tamaroh/maggie42/image/IMG_0094.jpg

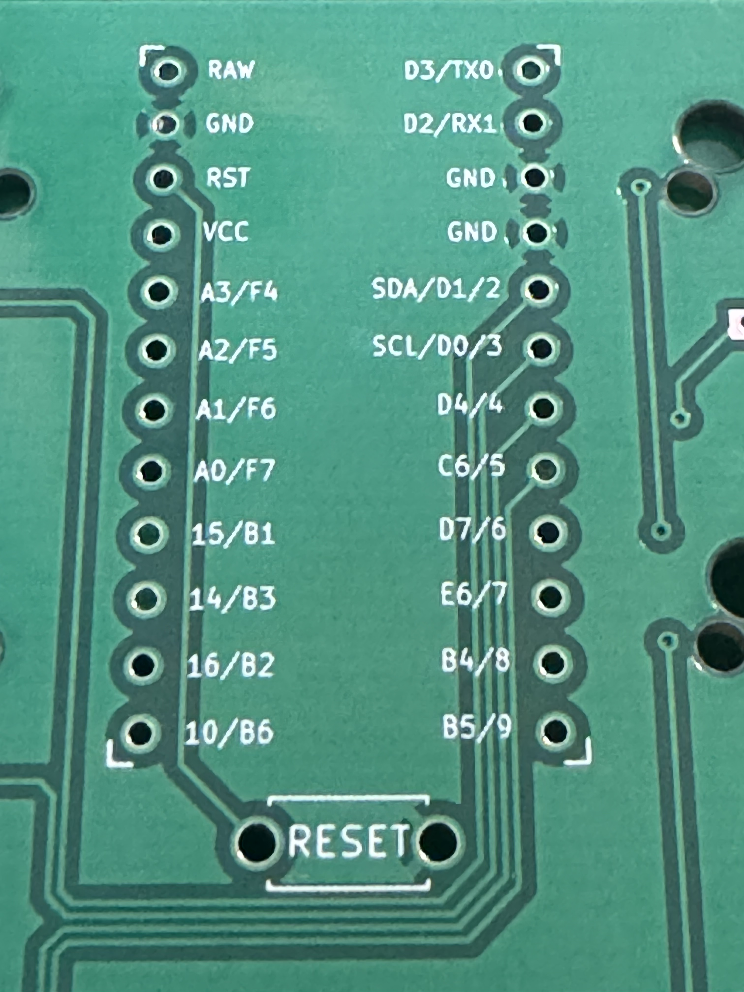
image/IMG_0094.jpg
